yuvve/e7020e_project/software/src/pwm.rs

use {
    crate::app::*,
    hal::{
        gpio::{Output, Pin, PushPull},
        pac::PWM0,
        pwm::*,
    },
    nrf52833_hal as hal,
};

pub const SEQUENCE_LENGTH: usize = 1000;
const SEQ_REFRESH: u32 = 10; // Extra periods per step
const MAX_DUTY: u16 = 10000;

pub type SeqBuffer = &'static mut [u16; 4*SEQUENCE_LENGTH];
pub type Pwm0 = Option<PwmSeq<PWM0, SeqBuffer, SeqBuffer>>;

pub(crate) fn init(
    pwm: PWM0,
    led_pin: Pin<Output<PushPull>>,
    haptic_pin: Pin<Output<PushPull>>,
) -> Pwm<PWM0> {
    let pwm = hal::pwm::Pwm::new(pwm);
    pwm.set_prescaler(Prescaler::Div16)
        .set_max_duty(MAX_DUTY)
        .set_output_pin(Channel::C0, led_pin)
        .set_output_pin(Channel::C1, haptic_pin)
        .set_counter_mode(CounterMode::Up)
        .set_load_mode(LoadMode::Individual)
        .set_step_mode(StepMode::Auto)
        .set_seq_refresh(Seq::Seq0, SEQ_REFRESH)
        .set_seq_refresh(Seq::Seq1, SEQ_REFRESH)
        .one_shot()
        .enable();
    pwm
}

pub(crate) fn load_pwm_sequence(cx: load_pwm_sequence::Context) {
    let (buf0, buf1, pwm) = cx.shared.pwm.take().unwrap().split();
    let seqbuf0 = buf0.unwrap();
    let seqbuf1 = buf1.unwrap();

    for i in 0..SEQUENCE_LENGTH {
        seqbuf0[i * 4] = LED_SEQUENCE[i];
        seqbuf0[i * 4 + 1] = HAPTIC_SEQUENCE[i];
        seqbuf0[i * 4 + 2] = EMPTY_SEQUENCE[i];
        seqbuf0[i * 4 + 3] = EMPTY_SEQUENCE[i];
    }
    seqbuf1.copy_from_slice(seqbuf0);
    let pwm = pwm.load(Some(seqbuf0), Some(seqbuf1), false).ok();
    *cx.shared.pwm = pwm;
}

pub(crate) fn start(cx: start_pwm::Context) {
    let pwm = cx.shared.pwm.as_ref().unwrap();
    pwm.start_seq(Seq::Seq0);
}

pub(crate) fn stop(cx: stop_pwm::Context) {
    let pwm = cx.shared.pwm.as_ref().unwrap();
    pwm.stop();
}

static EMPTY_SEQUENCE: [u16; SEQUENCE_LENGTH] = [0u16; SEQUENCE_LENGTH];

static LED_SEQUENCE: [u16; SEQUENCE_LENGTH] = [
    10000, 10000, 10000, 10000, 10000, 10000, 10000, 10000, 10000, 10000, 10000, 10000, 10000,
    10000, 10000, 10000, 10000, 10000, 10000, 10000, 10000, 10000, 10000, 10000, 10000, 10000,
    10000, 10000, 10000, 10000, 10000, 10000, 10000, 10000, 10000, 10000, 10000, 10000, 10000,
    10000, 10000, 10000, 10000, 10000, 10000, 10000, 10000, 10000, 10000, 10000, 10000, 10000,
    10000, 10000, 10000, 10000, 10000, 10000, 10000, 10000, 10000, 10000, 10000, 10000, 10000,
    10000, 10000, 10000, 10000, 10000, 10000, 10000, 10000, 10000, 10000, 10000, 10000, 10000,
    10000, 10000, 10000, 10000, 10000, 10000, 10000, 10000, 10000, 10000, 10000, 10000, 10000,
    10000, 10000, 10000, 10000, 10000, 10000, 10000, 10000, 10000, 9900, 9900, 9900, 9900, 9900,
    9900, 9900, 9900, 9900, 9900, 9900, 9900, 9900, 9900, 9900, 9900, 9900, 9900, 9900, 9900, 9900,
    9900, 9900, 9900, 9900, 9900, 9900, 9900, 9900, 9900, 9900, 9900, 9900, 9900, 9900, 9900, 9900,
    9900, 9900, 9900, 9900, 9900, 9900, 9900, 9900, 9900, 9900, 9900, 9900, 9900, 9900, 9900, 9900,
    9900, 9900, 9900, 9900, 9900, 9900, 9900, 9900, 9900, 9900, 9900, 9900, 9900, 9900, 9900, 9900,
    9900, 9900, 9900, 9900, 9900, 9900, 9900, 9900, 9900, 9900, 9900, 9900, 9900, 9900, 9900, 9900,
    9900, 9900, 9900, 9900, 9900, 9900, 9900, 9900, 9900, 9900, 9900, 9900, 9900, 9900, 9900, 9800,
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
    6961, 6956, 6951, 6946, 6941, 6936, 6931, 6926, 6921, 6916, 6911, 6906, 6901, 6896, 6891, 6886,
    6881, 6876, 6871, 6866, 6861, 6856, 6851, 6846, 6841, 6836, 6831, 6826, 6821, 6816, 6811, 6806,
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
];
